PhilippeSimier/Ruche/Autonomie/HorlogeRTC_eeprom.PNG

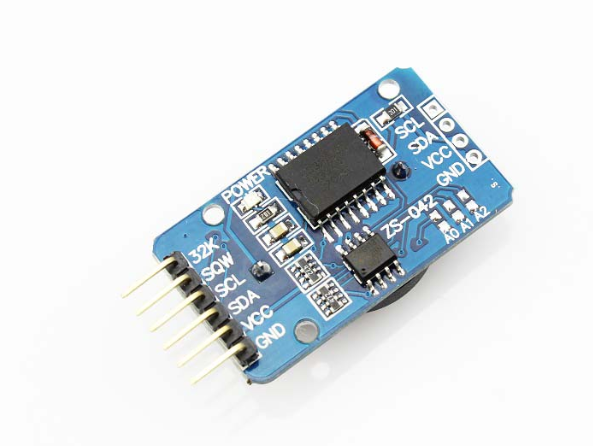
Autonomie/HorlogeRTC_eeprom.PNG
