PhilippeSimier/Ruche/Boitier/photos/20220206_170426.jpg

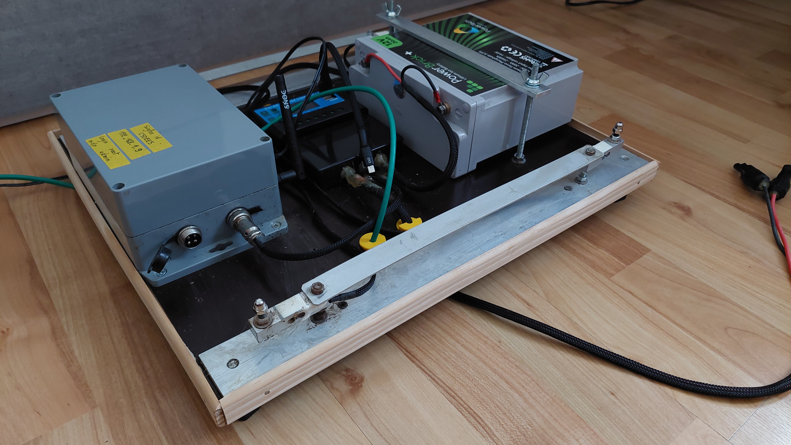
Boitier/photos/20220206_170426.jpg
