PhilippeSimier/Ruche/Boitier/photos/20220206_170449.jpg

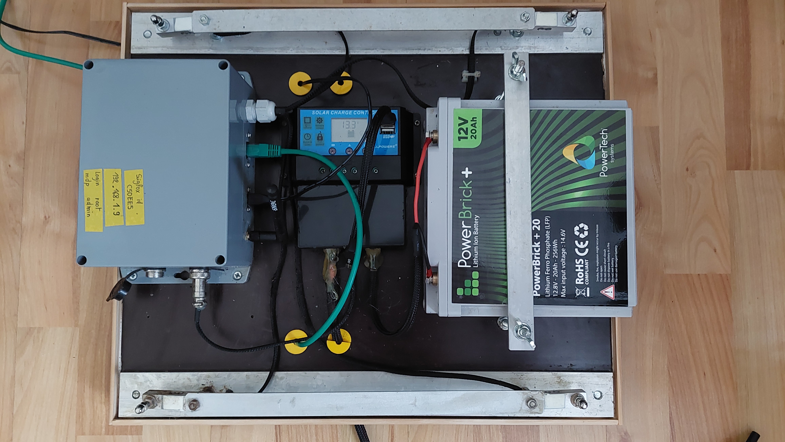
Boitier/photos/20220206_170449.jpg
