PhilippeSimier/Ruche/thingSpeak/reac_trop_froid.JPG

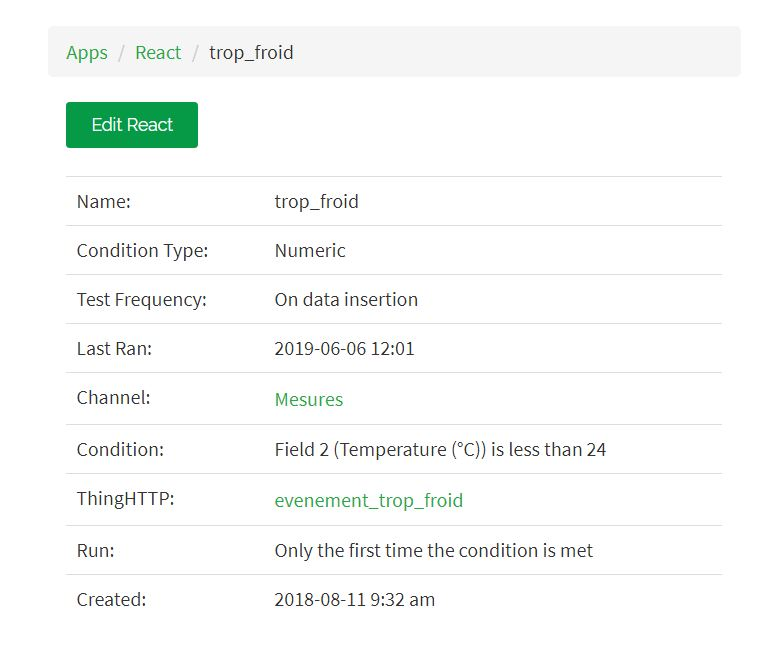
thingSpeak/reac_trop_froid.JPG
