PhilippeSimier/Ruche/thingSpeak/ThingHTTP.JPG

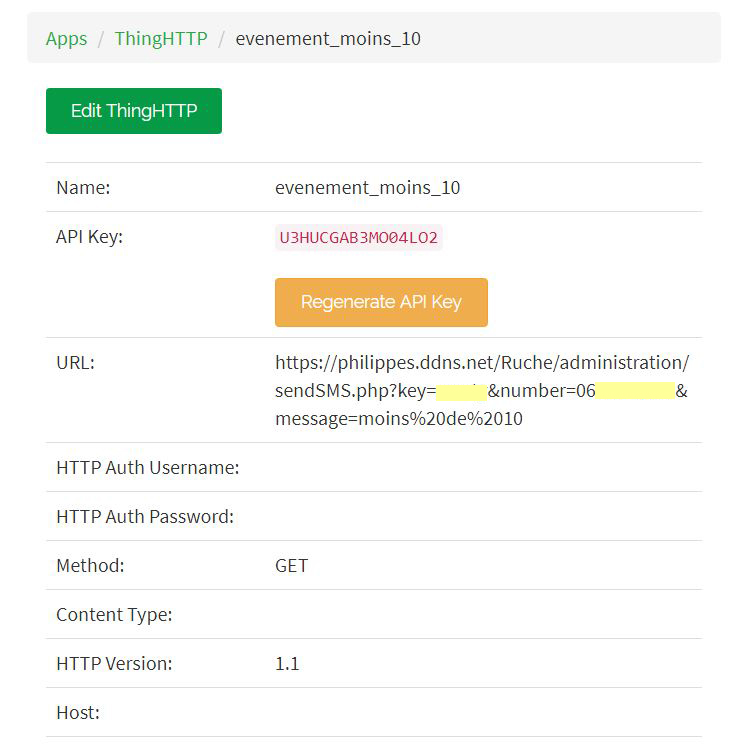
thingSpeak/ThingHTTP.JPG
