PhilippeSimier/Ruche/Sigfox/sigfox.h

/**
  * @file    sigfox.h
  * @author  Philippe SIMIER SNIR Touchard Washington
  * @date    23 juillet 2020
  * @details Communication avec le transmetteur BRKWS01
  *          sur le réseau Sigfox (commandes AT)
  *
  *
  */



#ifndef __SIGFOX__
#define __SIGFOX__

#include <iostream>
#include <string>
#include <iomanip>
#include <sstream>
#include "serie.h"

using namespace std;

class Sigfox
{
  public:

    Sigfox(const string _device, const bool _debug);
    ~Sigfox();
    string   tester(void);
    string   obtenirID(void);
    string   obtenirPAC(void);
    float    obtenirFreqEmi(void);
    float    obtenirFreqRec(void);
    float    obtenirTemp(void);
    void     obtenirTension(float &tension0, float &tension1);

    string   envoyer(const void* data, uint8_t size);
    string   modeSommeil(void);
    string   modeNormal(void);

  private:
    string device;
    bool debug;
    int fdSerie;
    char message[100];
};

#endif
