PhilippeSimier/Ruche/Capteurs/hx711.cpp

/**
 *  @file     hx711.cpp
 *  @author   Philippe SIMIER (Touchard Wahington le Mans)
 *  @license  BSD (see license.txt)
 *  @date     6 juin 2018 & 13 Juillet 2019
 *  @brief    Classe pour le composant HX711
 *  @version  2.0
*/

#include "hx711.h"

using namespace std;

/**
 * @brief hx711::hx711
 * @details Constructeur de la classe, initialise les attributs
 *          par défaut spi, scale, offset
 */

hx711::hx711(float _scale)
{
    /* Ouverture de spidev0.0 avec le  mode 0 et la vitesse max 1MHz */
    if (spi_open(&spi, "/dev/spidev0.0", 0, 1000000) < 0) {
        std::cout << "spi_open(): " << spi_errmsg(&spi) << std::endl;
        exit(1);
    }
    scale = _scale;
    offset = 0;
    bufferEmission[0] = 0xaa;
    bufferEmission[1] = 0xaa;
    bufferEmission[2] = 0xaa;
    bufferEmission[3] = 0xaa;
    bufferEmission[4] = 0xaa;
    bufferEmission[5] = 0xaa;
    bufferEmission[6] = 0xa8;   // 0xa8 gain = 64  0x80 gain = 128
}

/**
 * @brief hx711::~hx711
 * @details Destructeur de la classe
 */
hx711::~hx711()
{
    spi_close(&spi);

}


/**
 * @brief hx711::obtenirValeur()
 *
 * @details Permet d'obtenir la valeur brute de la conversion
 */
int hx711::obtenirValeur()
{
	unsigned char byte;
	int valeur = 0;

        unsigned char bufferReception[7];

        usleep(110000); // attente fin de conversion
        spi_transfer(&spi, bufferEmission, bufferReception, sizeof(bufferEmission));

	for (int i=0; i<6; i++){
	    for (int j=6; j>=0; j=j-2){
	    	byte = bufferReception[i] & (1<<j);
	    	byte >>= j;
	    	valeur = valeur | byte ;
	    	if ((j>0) | (i<5))
	            valeur = (valeur<<1);
	    }
	}

	// Gestion des valeurs négatives
	if (valeur > 0xf00000)
	    valeur = valeur | 0xfff00000;

	return valeur;
}

/**
 * @brief hx711::obtenirPoids()
 *
 * @details Permet d'obtenir la valeur du poids en unité de mesure (médiane de la série)
 * @input   nb nombre de valeur de la série de mesures (par défaut 11)
 * @return float la valeur du poids
 */


float hx711::obtenirPoids(int nb)
{

    int som = 0;
    vector<int> valeur;

    // Lecture de nb valeurs
    for (int i=0; i < nb; i++)
    {
        valeur.push_back(obtenirValeur());
    }

    // Tri des valeurs grâce à la fonction std::sort
    sort (valeur.begin(), valeur.end());

    // valeurBrute prend la mediane de la série
    valeurBrute = valeur.at(nb/2);

   // Calcul de la variance de la série
    variance = calculerVariance(valeur);

    return (float)(valeurBrute - offset)/scale;
}



/**
 * @brief hx711::effectuerTarage()
 *
 * @details Permet de mettre à jour la valeur de l'offset
 */

void  hx711::effectuerTarage()
{
    offset = obtenirValeur();
}

/**
 * @brief hx711::fixerEchelle()
 *
 * @details Permet de configurer l'échelle de mesure
 */

void hx711::fixerEchelle(float _scale)
{
    scale = _scale;
}


/**
 * @brief hx711::fixerOffset()
 *
 * @details Permet de configurer l'offset
 * Cette valeur est obtenue après tarage de la balance
 */

void hx711::fixerOffset(int _offset)
{
	offset = _offset;
}



/**
 * @brief hx711::obtenirOffset()
 *
 * @details Permet d'obtenir la valeur de l'offset
 * Cette valeur est obtenue après tarage de la balance
 */

int hx711::obtenirOffset()
{
	return offset;
}

/**
 * @brief hx711::obtenirOffset()
 *
 * @details Permet d'obtenir la valeur de la variance
 * Cette valeur est obtenue après une mesure du poids
 * Elle permet de quantifier la dispersion des mesures
 */

float hx711::obtenirVariance()
{
	return variance;
}

/**
 * @brief hx711::configurerGain()
 *
 * @details Permet de configurer la valeur du gain de l'amplificateur
 * pour le canal A deux valeurs possibles 128 ou 64
 */

void hx711::configurerGain(char gain)
{
    switch(gain){
	case 128:
	    bufferEmission[6] = 0x80; // 25 impulsions
            break;
        case 64:
	    bufferEmission[6] = 0xa8; // 27 impulsions
            break;
        default:
            bufferEmission[6] = 0xa8; // 27 impulsions

    }
}

/**
 * @brief hx711::fixerSlope()
 *
 * @details Permet de définir la valeur de la dérive du poids due à la température ambiante
 * @param   float la valeur du slope
 */

void hx711::fixerSlope(float _slope)
{
    slope = _slope;
}

/**
 * @brief hx711::fixerTempRef()
 *
 * @details Permet de définir la valeur de la température de référence 
 * @param   float la valeur du température de référence
 */

void hx711::fixerTempRef(float _tempRef)
{
    tempRef = _tempRef;
}


/**
 * @brief hx711::obtenirPoidsCorrige(float temp);
 *
 * @details Permet d'obtenir la valeur du poids corrigé en fonction de la températue
 * @param   float la valeur de la température ambiante
 */

float hx711::obtenirPoidsCorrige(float temp)
{
    float poids = obtenirPoids();
    float poidsCorrige = poids + slope * (tempRef - temp);
    return poidsCorrige;
}

float hx711::calculerMoyenne(const std::vector<int> &t)
{
    float k=0;
    unsigned int nb = t.size();
    for(unsigned int i=0 ; i<nb ; i++)
    {
        k = k+t[i];
    }

    k = k/nb;
    return k;
}

float hx711::calculerVariance(const std::vector<int> &t)
{
    float u;
    u = calculerMoyenne(t);

    float k = 0;
    for(unsigned int i=0 ; i<t.size() ; i++)
    {
        k = k + (t[i]-u)*(t[i]-u);
    }

    k = k/t.size();
    return k;
}
