PhilippeSimier/Ruche/Capteurs/testBH1750.cpp

/*!
    \file     testBH1750.cpp
    \author   Philippe SIMIER (Touchard Wahington le Mans)
    \license  BSD (see license.txt)
    \date     15 Aout 2018
    \brief    Programme pour test du capteur d'éclairement bh170
    \details
	compilation : g++ testBH1750.cpp i2c.cpp  bh1750.cpp -o testBH1750
    \version V1.0 First release
*/


#include <iostream>
#include <iomanip>
#include <unistd.h>
#include "bh1750.h"

using namespace std;

int main()
{
    system("clear");
    bh1750 capteur;
    float eclairement;
    cout << "Capteur d'éclairement" << endl;

    capteur.activer();
    capteur.reset();

    while(1){
        capteur.configurer(BH1750_CONTINUOUS_HIGH_RES_MODE_2);
        eclairement = capteur.obtenirLuminosite_Lux();
        // passage en résolution 1 lux si l'éclairement dépasse les 27000 Lux
        if (eclairement > 27000){
	    capteur.configurer(BH1750_CONTINUOUS_HIGH_RES_MODE);
        }
	cout << "Eclairement : " << fixed << setprecision (1) << capteur.obtenirLuminosite_Lux()  << " lx" << endl;
        sleep(1);

    }
    return 0;
}
