PhilippeSimier/Ruche/Capteurs/testBME280.cpp

/*******************************************************************************************
*   Compilation :  g++ testBME280.cpp i2c.cpp  bme280.cpp -o testBME280
*******************************************************************************************/

#include <iostream>
#include "bme280.h"
#include <unistd.h>

using namespace std;

int main()
{
    char adresse = 0x77;    // l'adresse du composant BME280
    bme280 capteur(adresse);
    if (!capteur.obtenirErreur()){

    	cout << "Capteur BME 280 présent sur le bus I2C" << endl;
        capteur.donnerAltitude(40);

        while(1){
    	    cout << " Température (C)  : " << fixed << setprecision (1) << capteur.obtenirTemperatureEnC() << " °C"<< endl;
    	    cout << " Température (F)  : " << fixed << setprecision (1) << capteur.obtenirTemperatureEnF() << " °F"<< endl;
    	    cout << " Pression         : " << fixed << setprecision (1) << capteur.obtenirPression() << " hPa"<< endl;
    	    cout << " Humidité         : " << fixed << setprecision (1) << capteur.obtenirHumidite() << " %"<< endl;
    	    cout << " Pression P0      : " << fixed << setprecision (1) << capteur.obtenirPression0() << " hPa"<< endl;
    	    cout << " Point de rosée   : " << fixed << setprecision (1) << capteur.obtenirPointDeRosee() << " °C"<< endl;
    	    sleep(1);

    	}
    }
    else{
	cout << " Le capteur BME280 n'est pas présent à l'adresse : 0x" << hex << (int)adresse << endl;
	capteur.version();
    }

    return 0;
}
